Settorezero/WePaRT/docs/LoRa32_use_UFL_antenna.jpg

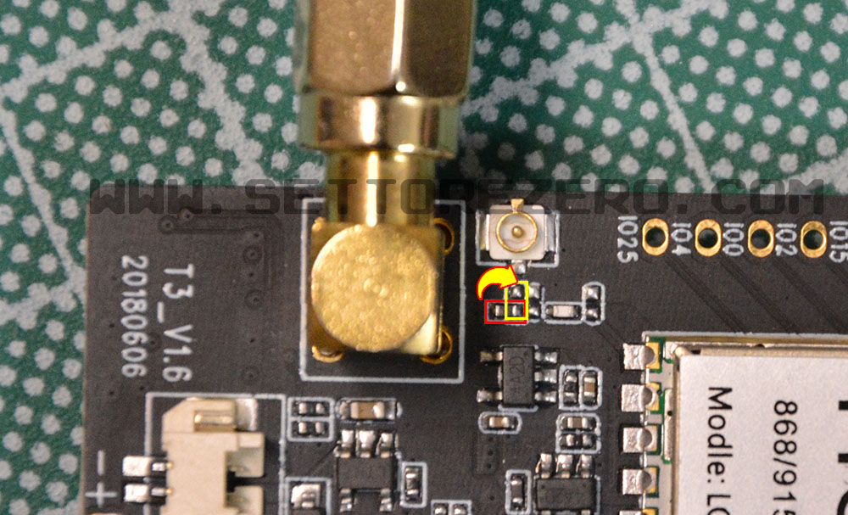
docs/LoRa32_use_UFL_antenna.jpg
