Settorezero/WePaRT/docs/SDS011_consented_mounting.png

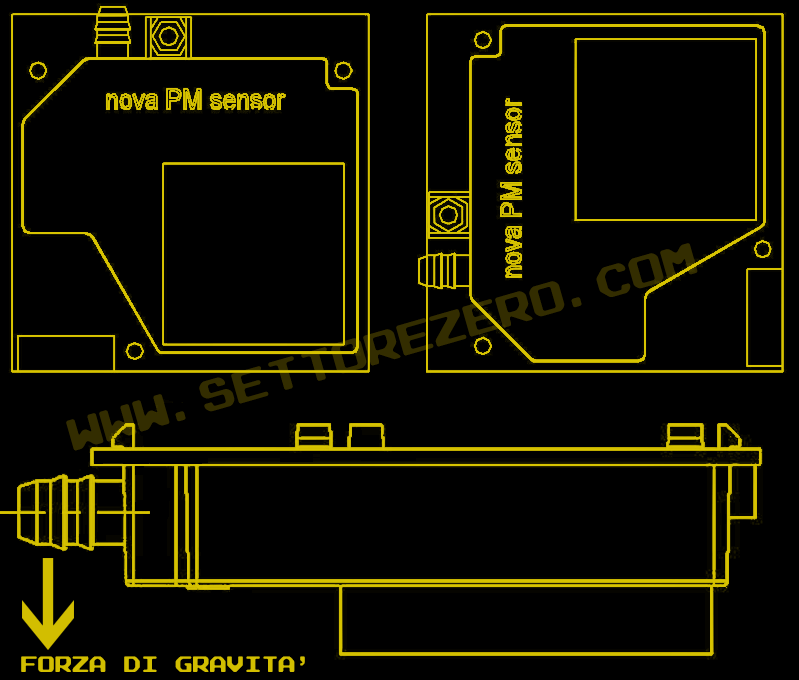
docs/SDS011_consented_mounting.png
