Settorezero/WePaRT/media/wepart_base_station_pic_01.jpg

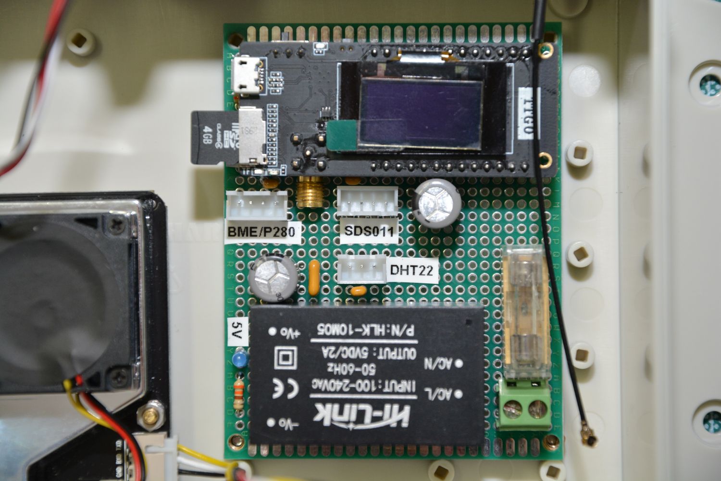
media/wepart_base_station_pic_01.jpg
