Settorezero/WePaRT/media/wepart_exhaust.jpg

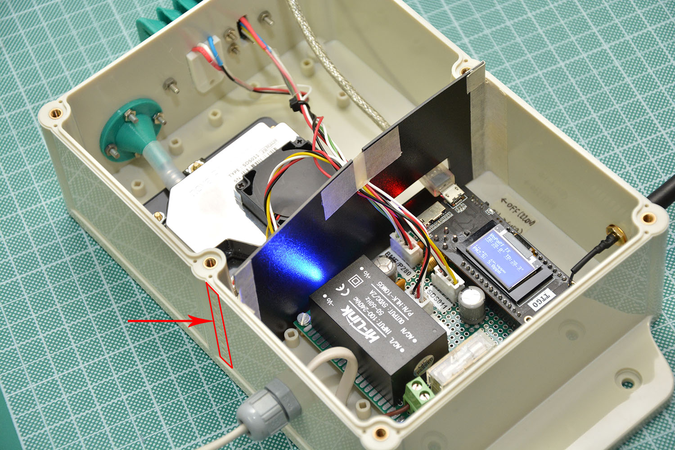
media/wepart_exhaust.jpg
