Settorezero/WePaRT/media/wepart_sds011_funnel.jpg

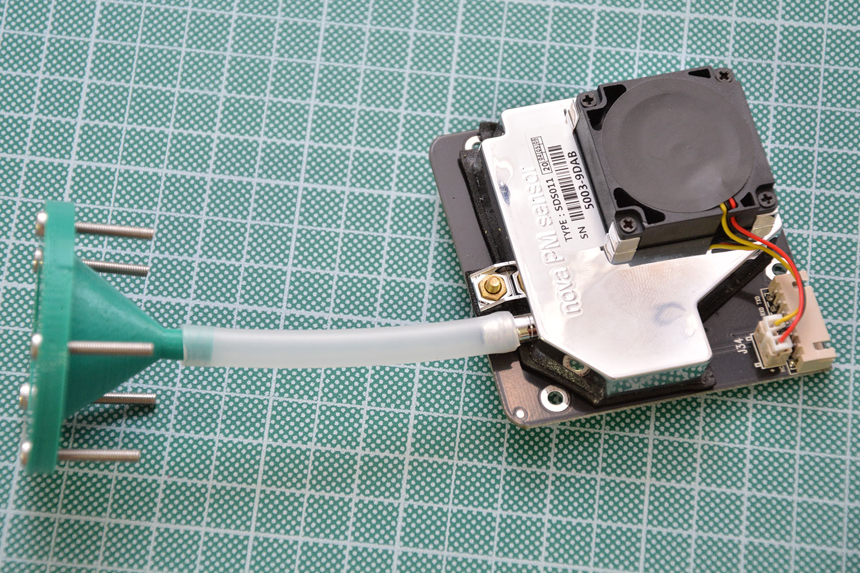
media/wepart_sds011_funnel.jpg
