Settorezero/WePaRT/media/wepart_sensors_external.jpg

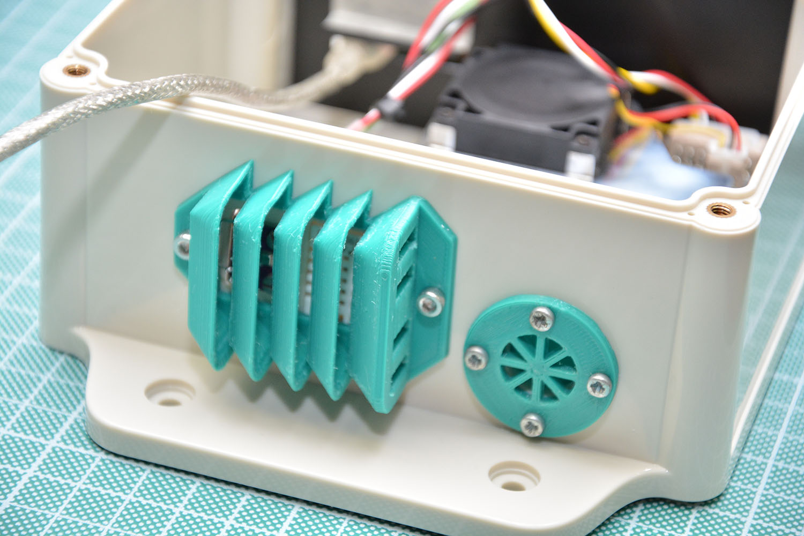
media/wepart_sensors_external.jpg
