Settorezero/WePaRT/media/wepart_sensors_internal.jpg

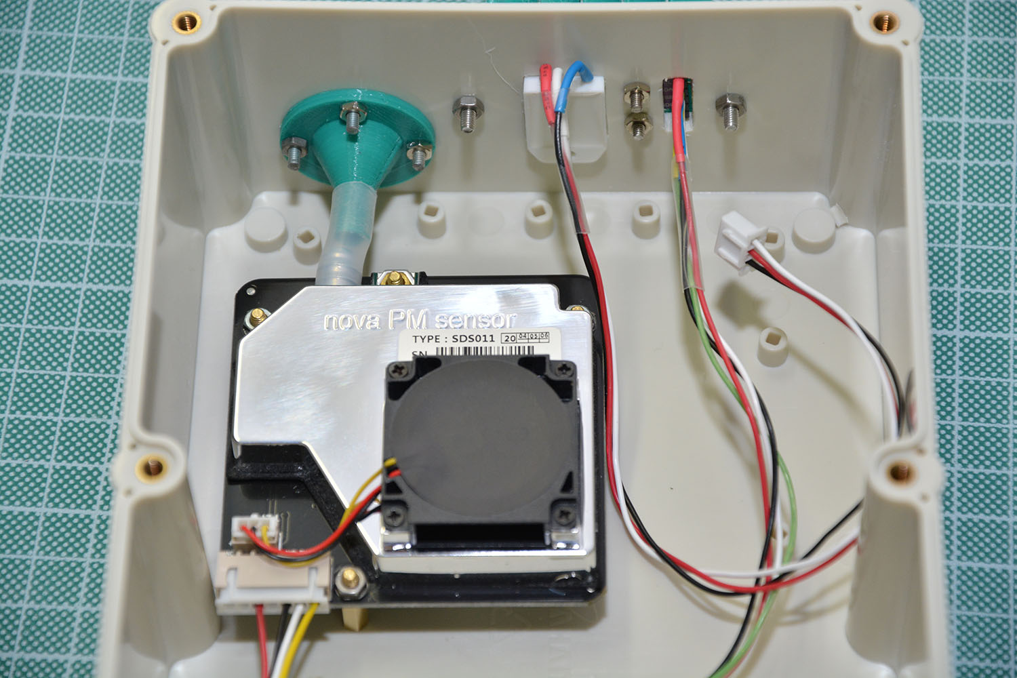
media/wepart_sensors_internal.jpg
