Settorezero/WePaRT/media/parts/BME280.png

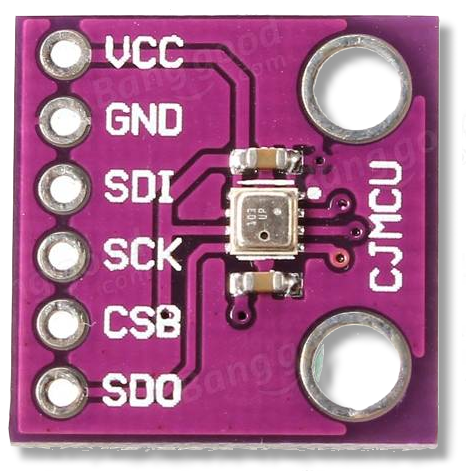
media/parts/BME280.png
