Settorezero/WePaRT/media/parts/DHT2222.png

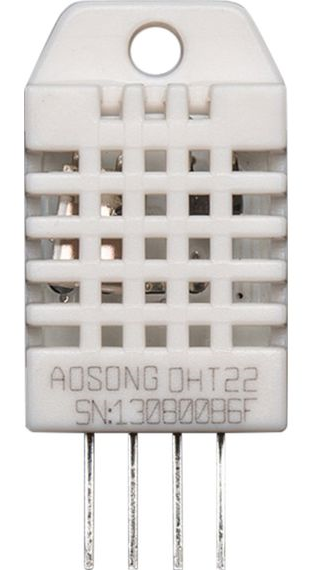
media/parts/DHT2222.png
