Settorezero/WePaRT/media/parts/SDS011.png

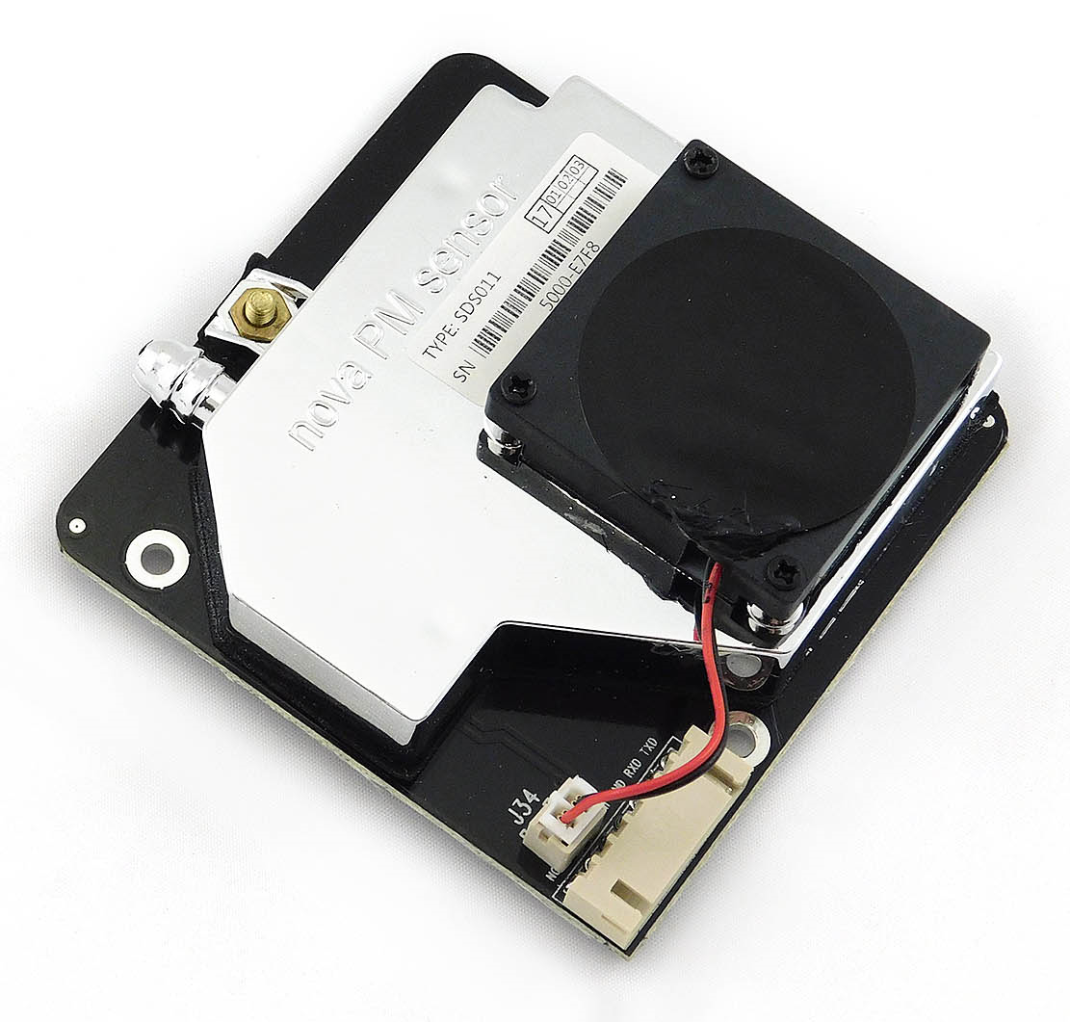
media/parts/SDS011.png
