Settorezero/WePaRT/media/parts/TTGO_LoRa32.png

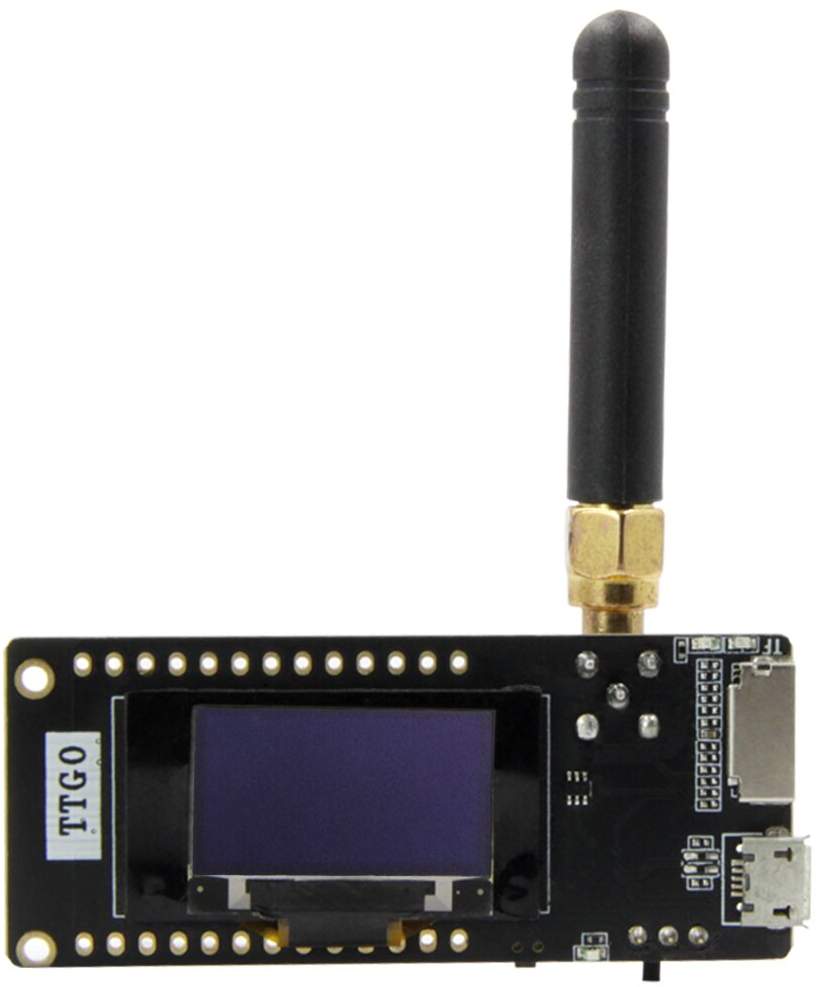
media/parts/TTGO_LoRa32.png
