Settorezero/WePaRT/arduino/wepart_remote_station/my_fonts.h

// Created by http://oleddisplay.squix.ch/ Consider a donation
// In case of problems make sure that you are using the font file with the correct version!
const uint8_t Monospaced_bold_11[] PROGMEM = {
  0x07, // Width: 7
  0x0E, // Height: 14
  0x20, // First Char: 32
  0xE0, // Numbers of Chars: 224

  // Jump Table:
  0xFF, 0xFF, 0x00, 0x07,  // 32:65535
  0x00, 0x00, 0x0A, 0x07,  // 33:0
  0x00, 0x0A, 0x09, 0x07,  // 34:10
  0x00, 0x13, 0x0D, 0x07,  // 35:19
  0x00, 0x20, 0x0C, 0x07,  // 36:32
  0x00, 0x2C, 0x0C, 0x07,  // 37:44
  0x00, 0x38, 0x0E, 0x07,  // 38:56
  0x00, 0x46, 0x07, 0x07,  // 39:70
  0x00, 0x4D, 0x0A, 0x07,  // 40:77
  0x00, 0x57, 0x0A, 0x07,  // 41:87
  0x00, 0x61, 0x0B, 0x07,  // 42:97
  0x00, 0x6C, 0x0B, 0x07,  // 43:108
  0x00, 0x77, 0x08, 0x07,  // 44:119
  0x00, 0x7F, 0x0A, 0x07,  // 45:127
  0x00, 0x89, 0x08, 0x07,  // 46:137
  0x00, 0x91, 0x0B, 0x07,  // 47:145
  0x00, 0x9C, 0x0E, 0x07,  // 48:156
  0x00, 0xAA, 0x0E, 0x07,  // 49:170
  0x00, 0xB8, 0x0E, 0x07,  // 50:184
  0x00, 0xC6, 0x0E, 0x07,  // 51:198
  0x00, 0xD4, 0x0E, 0x07,  // 52:212
  0x00, 0xE2, 0x0E, 0x07,  // 53:226
  0x00, 0xF0, 0x0E, 0x07,  // 54:240
  0x00, 0xFE, 0x0D, 0x07,  // 55:254
  0x01, 0x0B, 0x0E, 0x07,  // 56:267
  0x01, 0x19, 0x0E, 0x07,  // 57:281
  0x01, 0x27, 0x08, 0x07,  // 58:295
  0x01, 0x2F, 0x08, 0x07,  // 59:303
  0x01, 0x37, 0x0E, 0x07,  // 60:311
  0x01, 0x45, 0x0E, 0x07,  // 61:325
  0x01, 0x53, 0x0E, 0x07,  // 62:339
  0x01, 0x61, 0x09, 0x07,  // 63:353
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
  0x00,0x00,0xF8,0x07,0xF8,0x07,0x48,0x00,0x48,0x00,0x48,0x00,0x08, // 70
  0x00,0x00,0xE0,0x01,0xF0,0x03,0x18,0x06,0x88,0x04,0x88,0x07,0x90,0x07,  // 71
  0x00,0x00,0xF8,0x07,0xF8,0x07,0x40,0x00,0x40,0x00,0xF8,0x07,0xF8,0x07,  // 72
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
};
