Settorezero/WePaRT/arduino/wepart_base_station/images.h

/*
 * Logo Images
 * draw a 1bit bitmap: pixel ON=white pixel OFF=black
 * convert using:
 * https://convertio.co/it/bmp-xbm/
 * or
 * https://www.online-utility.org/image_converter.jsp (choose XBM)
 */

#define SZ_logo_width 64
#define SZ_logo_height 64
const uint8_t PROGMEM SZ_logo [] = {
  0xFF, 0xFF, 0xFF, 0xFF, 0xFF, 0xFF, 0xFF, 0xFF, 0xFF, 0xFF, 0xFF, 0xFF, 
  0xFF, 0xFF, 0xFF, 0xFF, 0x03, 0x00, 0x00, 0x00, 0x00, 0x00, 0x00, 0xC0, 
  0x03, 0x00, 0x00, 0x00, 0x00, 0x00, 0x00, 0xC0, 0x03, 0x00, 0x00, 0x00, 
  0x00, 0x00, 0x00, 0xC0, 0x03, 0x00, 0x00, 0x00, 0x00, 0x00, 0x00, 0xC0, 
  0x03, 0x00, 0x00, 0x00, 0x00, 0x00, 0x00, 0xC0, 0x03, 0x00, 0x00, 0x00, 
  0x00, 0x00, 0x00, 0xC0, 0x03, 0x00, 0x00, 0x00, 0x00, 0x00, 0x00, 0xC0, 
  0x03, 0x00, 0x00, 0x00, 0x00, 0x00, 0x00, 0xC0, 0x03, 0x00, 0x00, 0x00, 
  0x00, 0x00, 0x00, 0xC0, 0x03, 0x00, 0x00, 0x00, 0x00, 0x00, 0x00, 0xC0, 
  0x03, 0x00, 0x00, 0x00, 0x00, 0x00, 0x00, 0xC0, 0x03, 0x00, 0x00, 0x00, 
  0x00, 0x00, 0x00, 0xC0, 0x03, 0x00, 0x00, 0x00, 0x00, 0x00, 0x00, 0xC0, 
  0x03, 0x00, 0x00, 0x00, 0x00, 0x00, 0x00, 0xC0, 0x03, 0x00, 0x00, 0x00, 
  0x00, 0x00, 0x00, 0xC0, 0x03, 0x00, 0x00, 0x00, 0x00, 0xFE, 0x07, 0xC0, 
  0x03, 0x00, 0x00, 0x00, 0x00, 0xFF, 0x0F, 0xC0, 0x03, 0x00, 0x00, 0x00, 
  0xE0, 0xFF, 0x7F, 0xC0, 0x03, 0xF8, 0xFF, 0x1F, 0xE0, 0xFF, 0x7F, 0xC0, 
  0x03, 0xFC, 0xFF, 0x3F, 0x00, 0xFF, 0x0F, 0xC0, 0x03, 0xFE, 0xFF, 0x7F, 
  0xE0, 0xFF, 0x7F, 0xC0, 0x03, 0xFE, 0x81, 0x7F, 0xE0, 0xFF, 0x7F, 0xC0, 
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
  0x00, 0x00, 0x00, 0x70, 0x80, 0x03, 0x00, 0x00, 0x00, 0x00, 0xC0, 0xFF, 
  0x00, 0x00, 0x00, 0x00, 0x00, 0x0C, 0x00, 0x0C, 0x00, 0x00, 0x00, 0x00, 
  0x3C, 0x00, 0x0F, 0x00, 0x00, 0x00, 0x00, 0xF0, 0xFF, 0x03, 0x00, 0x00, 
  0x00, 0x00, 0x80, 0x7F, 0x00, 0x00, 0x00, 0x00, };
